MZMurad/X-band_Transmitter_Thesis_Files/Data/SpectrumAn_Data/2026-04-28_14-01-11_M2-022_Mixer_DownConv_LO-x_RF_-30dBm_Span_10MHz_RBW_100kHz.png

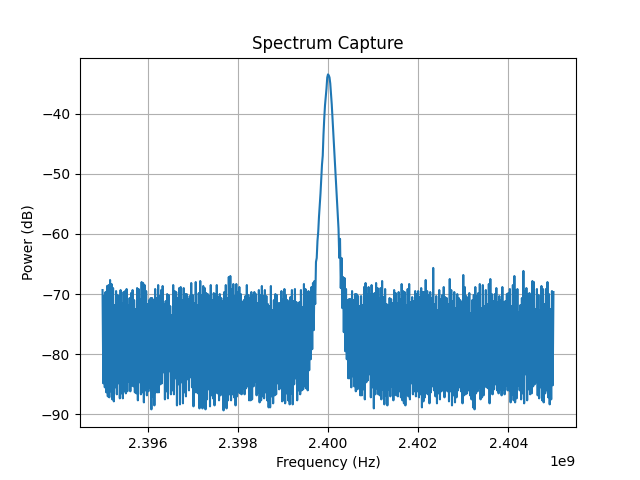
Data/SpectrumAn_Data/2026-04-28_14-01-11_M2-022_Mixer_DownConv_LO-x_RF_-30dBm_Span_10MHz_RBW_100kHz.png
