MZMurad/X-band_Transmitter_Thesis_Files/Data/SpectrumAn_Data/2026-04-28_14-03-07_M2-022_Mixer_LO_Span_10MHz_RBW_100kHz.png

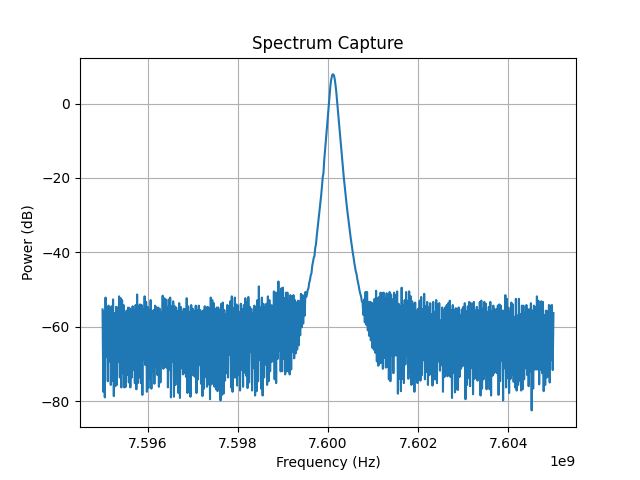
Data/SpectrumAn_Data/2026-04-28_14-03-07_M2-022_Mixer_LO_Span_10MHz_RBW_100kHz.png
