MZMurad/X-band_Transmitter_Thesis_Files/Data/SpectrumAn_Data/2026-04-28_14-05-14_M2-022_Mixer_RF_Span_10MHz_RBW_100kHz.png

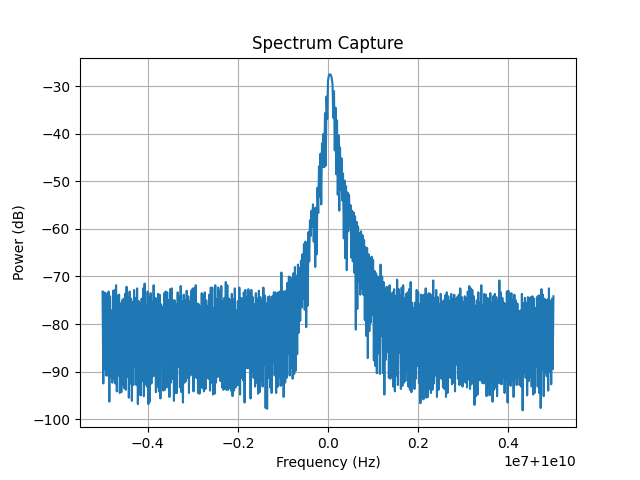
Data/SpectrumAn_Data/2026-04-28_14-05-14_M2-022_Mixer_RF_Span_10MHz_RBW_100kHz.png
