MZMurad/X-band_Transmitter_Thesis_Files/Data/SpectrumAn_Data/2026-04-28_14-42-43_Composite_Mixer_Span_Full_RBW_100kHz.png

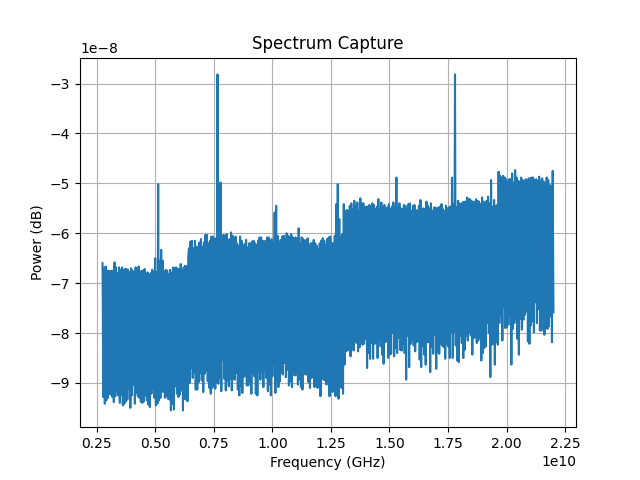
Data/SpectrumAn_Data/2026-04-28_14-42-43_Composite_Mixer_Span_Full_RBW_100kHz.png
