MZMurad/X-band_Transmitter_Thesis_Files/Data/SpectrumAn_Data/2026-04-28_14-44-34_Composite_Mixer_Span_500MHz_RBW_5MHz.png

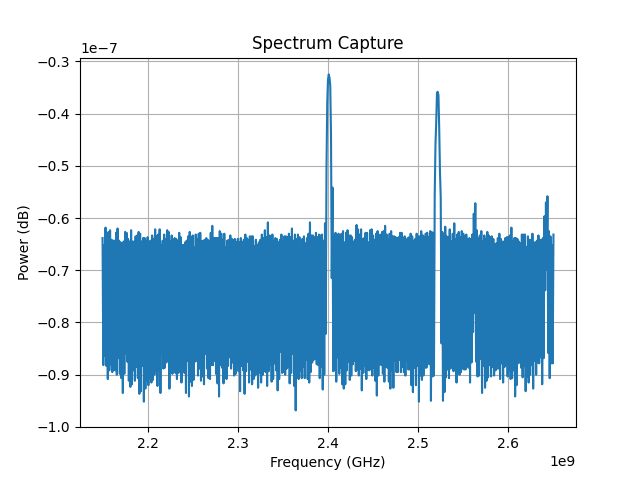
Data/SpectrumAn_Data/2026-04-28_14-44-34_Composite_Mixer_Span_500MHz_RBW_5MHz.png
