MZMurad/X-band_Transmitter_Thesis_Files/Data/SpectrumAn_Data/2026-04-28_14-51-12_Composite_Mixer_CW_IF_Span_10MHz_RBW_5MHz.png

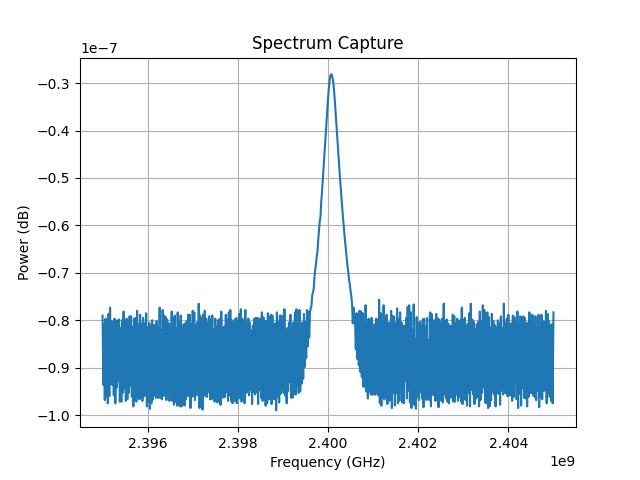
Data/SpectrumAn_Data/2026-04-28_14-51-12_Composite_Mixer_CW_IF_Span_10MHz_RBW_5MHz.png
