MZMurad/X-band_Transmitter_Thesis_Files/Data/SpectrumAn_Data/2026-04-28_14-57-12_Composite_Mixer_SDR_FullCapture_Span_1MHz_RBW_10kHz.png

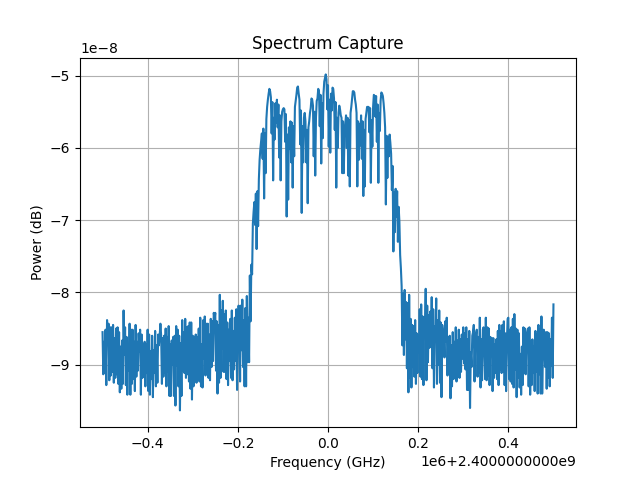
Data/SpectrumAn_Data/2026-04-28_14-57-12_Composite_Mixer_SDR_FullCapture_Span_1MHz_RBW_10kHz.png
