MZMurad/X-band_Transmitter_Thesis_Files/Data/SpectrumAn_Data/2026-04-28_16-52-47_PLL_Amp_LO_Span_Full_RBW_100kHz.png

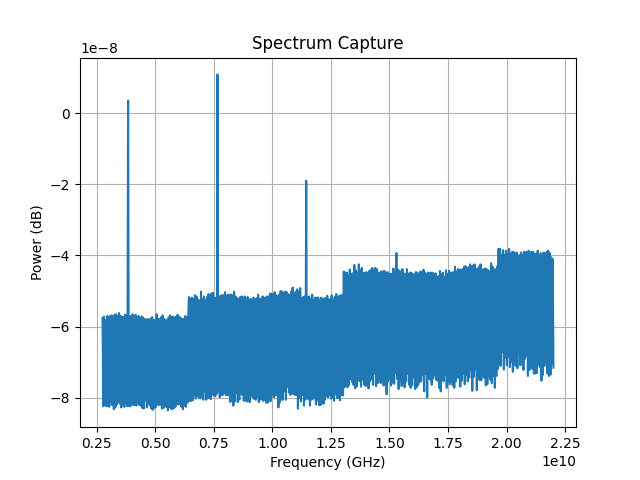
Data/SpectrumAn_Data/2026-04-28_16-52-47_PLL_Amp_LO_Span_Full_RBW_100kHz.png
