MZMurad/X-band_Transmitter_Thesis_Files/Data/SpectrumAn_Data/Mixer_Spectrum/2026-05-18_16-15-24_SDR_Upconverted_Spectrum.png

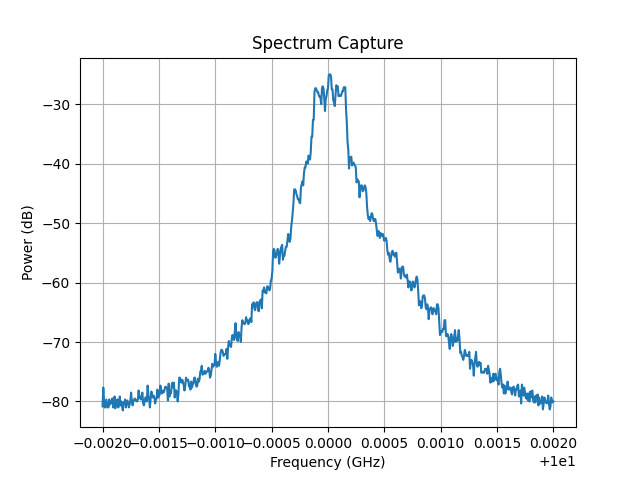
Data/SpectrumAn_Data/Mixer_Spectrum/2026-05-18_16-15-24_SDR_Upconverted_Spectrum.png
