MZMurad/X-band_Transmitter_Thesis_Files/Data/SpectrumAn_Data/Mixer_Spectrum/2026-05-18_16-33-44_SDR_Upconverted_Spectrum_Spa_1MHz_RBW30kHz.png

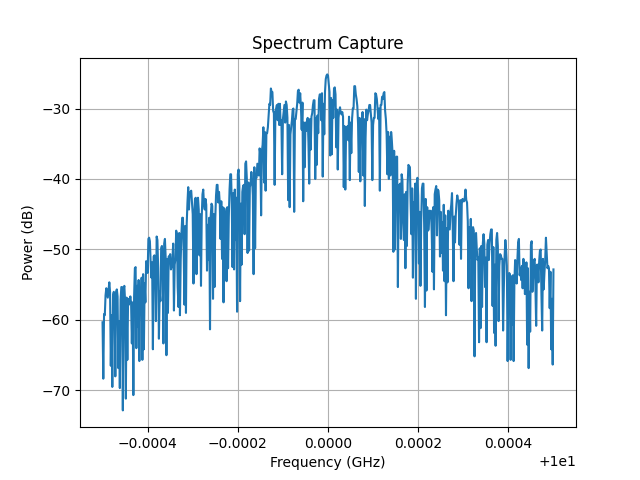
Data/SpectrumAn_Data/Mixer_Spectrum/2026-05-18_16-33-44_SDR_Upconverted_Spectrum_Spa_1MHz_RBW30kHz.png
