MZMurad/X-band_Transmitter_Thesis_Files/Data/SpectrumAn_Data/Mixer_Spectrum/2026-05-18_16-59-57_SDR_Composite_Mixer_Spectrum_Spa_1MHz_RBW_30kHz.png

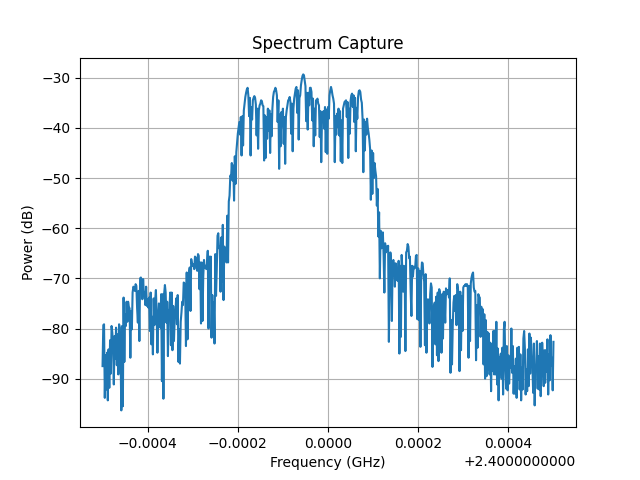
Data/SpectrumAn_Data/Mixer_Spectrum/2026-05-18_16-59-57_SDR_Composite_Mixer_Spectrum_Spa_1MHz_RBW_30kHz.png
