MZMurad/X-band_Transmitter_Thesis_Files/Data/SpectrumAn_Data/Mixer_Spectrum/2026-05-18_17-08-34_SDR_Composite_Mixer_Spectrum_Spa_1MHz_RBW_10kHz.png

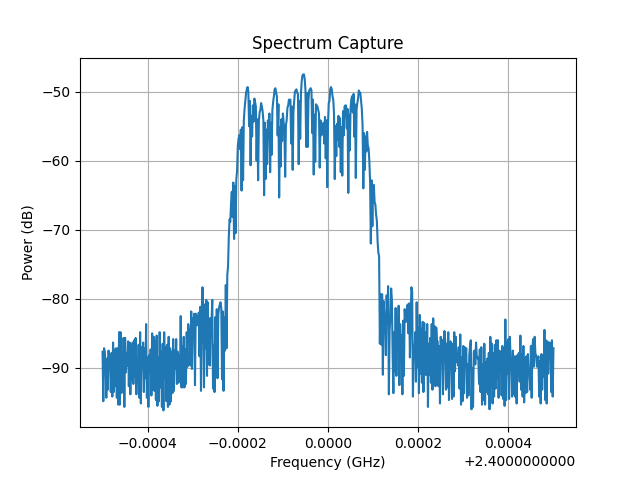
Data/SpectrumAn_Data/Mixer_Spectrum/2026-05-18_17-08-34_SDR_Composite_Mixer_Spectrum_Spa_1MHz_RBW_10kHz.png
