MZMurad/X-band_Transmitter_Thesis_Files/Data/SpectrumAn_Data/Mixer_Spectrum/2026-05-18_17-30-45_Mixer_CW_Spectrum_Spa_6GHz_RBW_100kHz.png

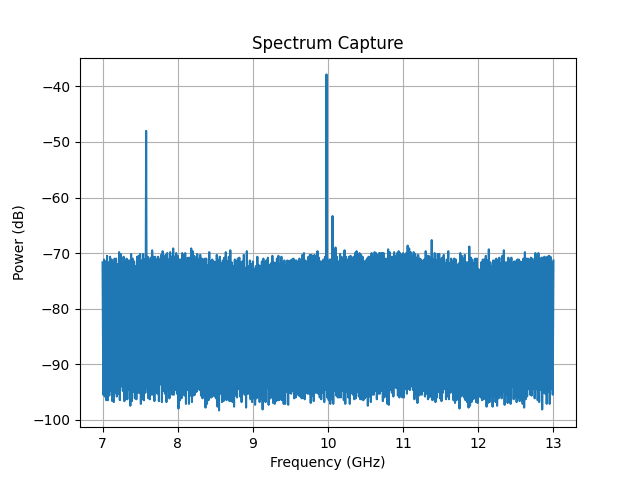
Data/SpectrumAn_Data/Mixer_Spectrum/2026-05-18_17-30-45_Mixer_CW_Spectrum_Spa_6GHz_RBW_100kHz.png
