MZMurad/X-band_Transmitter_Thesis_Files/Data/SpectrumAn_Data/PLL_Filter_Test/SDR_Test/2026-05-12_14-50-37_TX_SDR_Spectrum.png

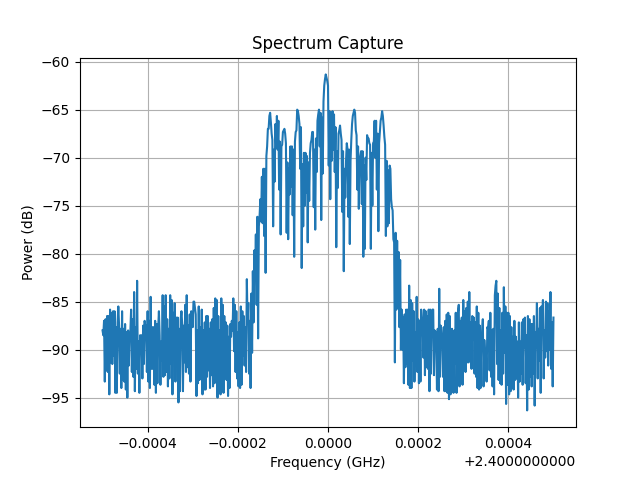
Data/SpectrumAn_Data/PLL_Filter_Test/SDR_Test/2026-05-12_14-50-37_TX_SDR_Spectrum.png
