MZMurad/X-band_Transmitter_Thesis_Files/Data/SpectrumAn_Data/PLL_Span_50MHz_RBW_3kHz.png

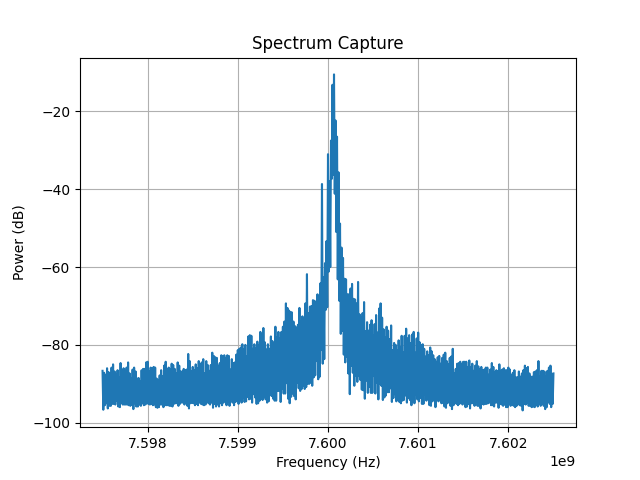
Data/SpectrumAn_Data/PLL_Span_50MHz_RBW_3kHz.png
