MZMurad/X-band_Transmitter_Thesis_Files/Data/SpectrumAn_Data/QPSK_Test/2026-05-31_18-19-41_SDR_Spectrum_Spa_5MHz_RBW_30kHz_MAXHOLD.png

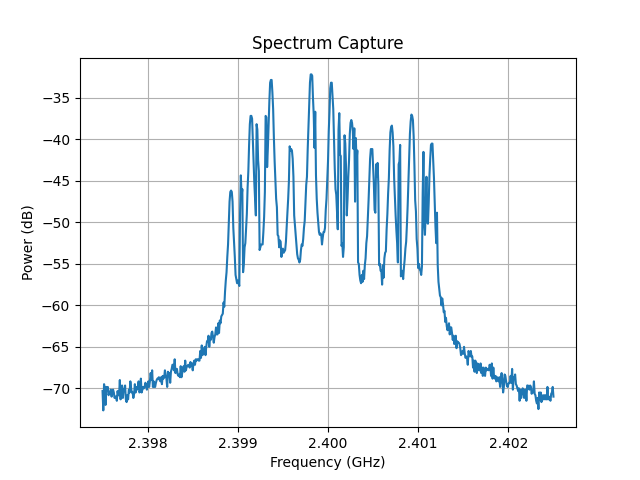
Data/SpectrumAn_Data/QPSK_Test/2026-05-31_18-19-41_SDR_Spectrum_Spa_5MHz_RBW_30kHz_MAXHOLD.png
