MZMurad/X-band_Transmitter_Thesis_Files/Data/VNA_Capture/2X10dBAtten.png

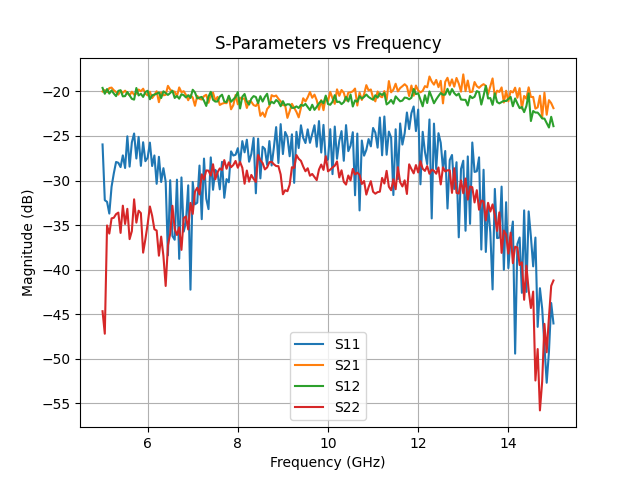
Data/VNA_Capture/2X10dBAtten.png
