MZMurad/X-band_Transmitter_Thesis_Files/Data/VNA_Capture/10dB_CalKit_Atten.png

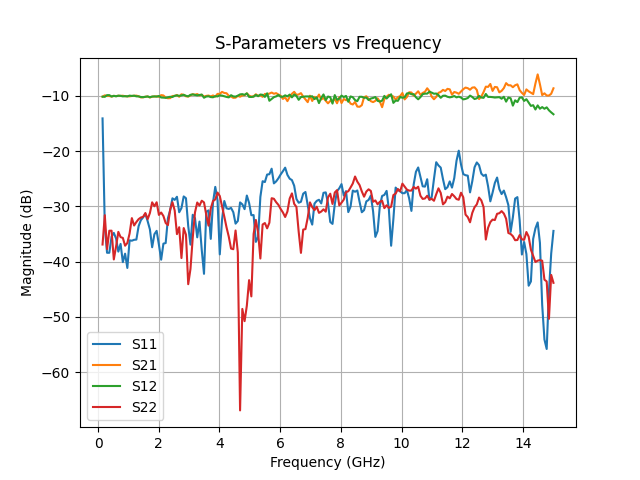
Data/VNA_Capture/10dB_CalKit_Atten.png
