MZMurad/X-band_Transmitter_Thesis_Files/Data/SpectrumAn_Data/2026-04-05_14-34-03_TestSpectrumCapture.csv

Date: 2026-04-05_14-34-03
Center Frequency (Hz): 7600000000.0
Span (Hz): 9700000000.0
RBW (Hz): 2000000.0
ID: 8562A GPIB0::18::INSTR
Frequency (Hz) | Power (dBm)
2.750000000000000000e+09 | -4.382999999999999829e+01
2.766166666666666508e+09 | -7.132999999999999829e+01
2.782333333333333492e+09 | -4.415999999999999659e+01
2.798500000000000000e+09 | -7.215999999999999659e+01
2.814666666666666508e+09 | -4.315999999999999659e+01
2.830833333333333492e+09 | -7.215999999999999659e+01
2.847000000000000000e+09 | -4.300000000000000000e+01
2.863166666666666508e+09 | -7.065999999999999659e+01
2.879333333333333492e+09 | -4.350000000000000000e+01
2.895500000000000000e+09 | -7.432999999999999829e+01
2.911666666666666508e+09 | -4.265999999999999659e+01
2.927833333333333492e+09 | -7.565999999999999659e+01
2.944000000000000000e+09 | -4.165999999999999659e+01
2.960166666666666508e+09 | -7.350000000000000000e+01
2.976333333333333492e+09 | -4.382999999999999829e+01
2.992500000000000000e+09 | -7.300000000000000000e+01
3.008666666666666508e+09 | -4.432999999999999829e+01
3.024833333333333492e+09 | -7.315999999999999659e+01
3.041000000000000000e+09 | -4.482999999999999829e+01
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
