MZMurad/X-band_Transmitter_Thesis_Files/Data/SpectrumAn_Data/PLL_Filter_Test/2026-05-12_14-18-42_PLL_PAmp_Test_Filter_Span_9.7GHz_RBW_2MHz_Distortion_Issue.csv

Date: 2026-05-12_14-18-42
Center Frequency (Hz): 7600000000.0
Span (Hz): 9700000000.0
RBW (Hz): 2000000.0
ID: 8562A GPIB0::18::INSTR
Frequency (Hz) | Power (dBm)
2.750000000000000000e+09 | -4.265999999999999659e+01
2.766166666666666508e+09 | -7.150000000000000000e+01
2.782333333333333492e+09 | -4.365999999999999659e+01
2.798500000000000000e+09 | -7.365999999999999659e+01
2.814666666666666508e+09 | -4.315999999999999659e+01
2.830833333333333492e+09 | -7.350000000000000000e+01
2.847000000000000000e+09 | -4.200000000000000000e+01
2.863166666666666508e+09 | -7.065999999999999659e+01
2.879333333333333492e+09 | -4.350000000000000000e+01
2.895500000000000000e+09 | -6.832999999999999829e+01
2.911666666666666508e+09 | -4.215999999999999659e+01
2.927833333333333492e+09 | -7.082999999999999829e+01
2.944000000000000000e+09 | -4.082999999999999829e+01
2.960166666666666508e+09 | -7.282999999999999829e+01
2.976333333333333492e+09 | -4.365999999999999659e+01
2.992500000000000000e+09 | -7.265999999999999659e+01
3.008666666666666508e+09 | -4.315999999999999659e+01
3.024833333333333492e+09 | -7.250000000000000000e+01
3.041000000000000000e+09 | -4.365999999999999659e+01
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
