MZMurad/X-band_Transmitter_Thesis_Files/Data/SpectrumAn_Data/PLL_Filter_Test/2026-05-12_14-36-30_PLL_PAmp_PFILTER_BeforeAmp_Test_Filter_Span_9.7GHz_RBW_2MHz_Distortion_Issue.csv

Date: 2026-05-12_14-36-30
Center Frequency (Hz): 7600000000.0
Span (Hz): 9700000000.0
RBW (Hz): 2000000.0
ID: 8562A GPIB0::18::INSTR
Frequency (Hz) | Power (dBm)
2.750000000000000000e+09 | -4.332999999999999829e+01
2.766166666666666508e+09 | -6.850000000000000000e+01
2.782333333333333492e+09 | -4.350000000000000000e+01
2.798500000000000000e+09 | -7.015999999999999659e+01
2.814666666666666508e+09 | -4.100000000000000000e+01
2.830833333333333492e+09 | -6.815999999999999659e+01
2.847000000000000000e+09 | -4.300000000000000000e+01
2.863166666666666508e+09 | -7.132999999999999829e+01
2.879333333333333492e+09 | -4.332999999999999829e+01
2.895500000000000000e+09 | -7.165999999999999659e+01
2.911666666666666508e+09 | -4.215999999999999659e+01
2.927833333333333492e+09 | -7.115999999999999659e+01
2.944000000000000000e+09 | -4.250000000000000000e+01
2.960166666666666508e+09 | -6.900000000000000000e+01
2.976333333333333492e+09 | -4.182999999999999829e+01
2.992500000000000000e+09 | -7.182999999999999829e+01
3.008666666666666508e+09 | -4.350000000000000000e+01
3.024833333333333492e+09 | -7.150000000000000000e+01
3.041000000000000000e+09 | -4.300000000000000000e+01
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
