MZMurad/X-band_Transmitter_Thesis_Files/Data/SpectrumAn_Data/PLL_Filter_Test/2026-05-12_14-36-30_PLL_PAmp_PFILTER_BeforeAmp_Test_Filter_Span_9.7GHz_RBW_2MHz_Distortion_Issue.png

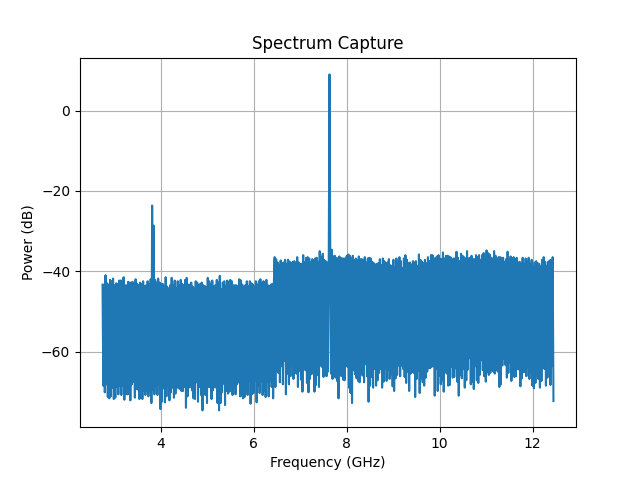
Data/SpectrumAn_Data/PLL_Filter_Test/2026-05-12_14-36-30_PLL_PAmp_PFILTER_BeforeAmp_Test_Filter_Span_9.7GHz_RBW_2MHz_Distortion_Issue.png
