MZMurad/X-band_Transmitter_Thesis_Files/Data/VNA_Capture/Amplifier_Test1_NoAtten_Pin_-25dB.png

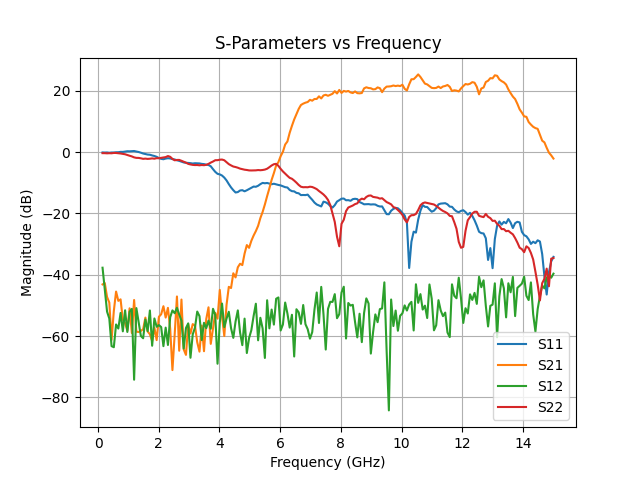
Data/VNA_Capture/Amplifier_Test1_NoAtten_Pin_-25dB.png
