MZMurad/X-band_Transmitter_Thesis_Files/Data/VNA_Capture/Amplifier_Test2_Atten_-10dB_Pin_-10dB.png

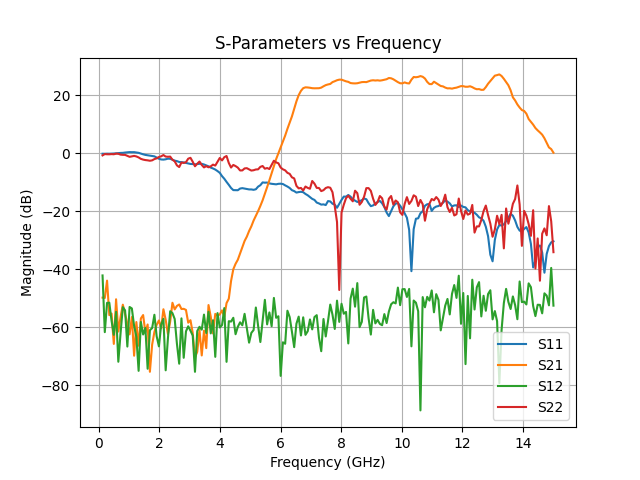
Data/VNA_Capture/Amplifier_Test2_Atten_-10dB_Pin_-10dB.png
