MZMurad/X-band_Transmitter_Thesis_Files/Data/VNA_Capture/Amplifier_Testt3_Pin_-10dB.png

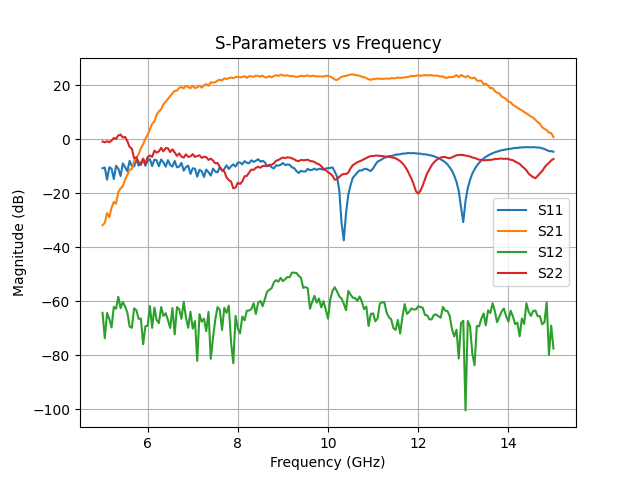
Data/VNA_Capture/Amplifier_Testt3_Pin_-10dB.png
