MZMurad/X-band_Transmitter_Thesis_Files/Data/SpectrumAn_Data/2026-04-28_17-56-01_PLL_Amp_LO_Span_9.7GHz_RBW_100kHz_Harmonics_Issue.png

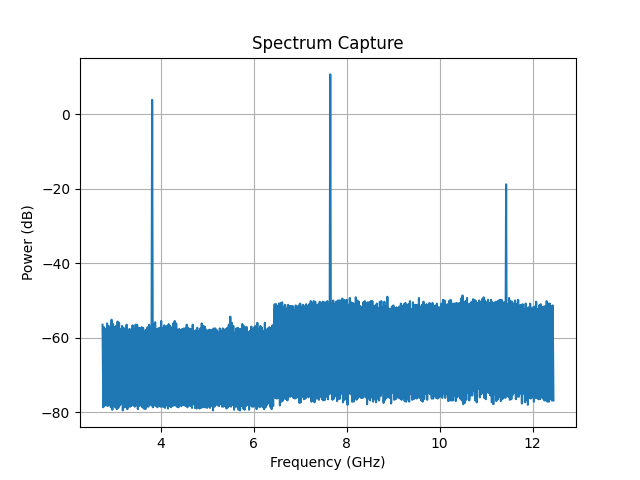
Data/SpectrumAn_Data/2026-04-28_17-56-01_PLL_Amp_LO_Span_9.7GHz_RBW_100kHz_Harmonics_Issue.png
