MZMurad/X-band_Transmitter_Thesis_Files/Data/SpectrumAn_Data/2026-04-28_18-13-17_PLL_Mixer_SDR_Issue_Span_14GHz_RBW_30kHz_Harmonics_Issue.png

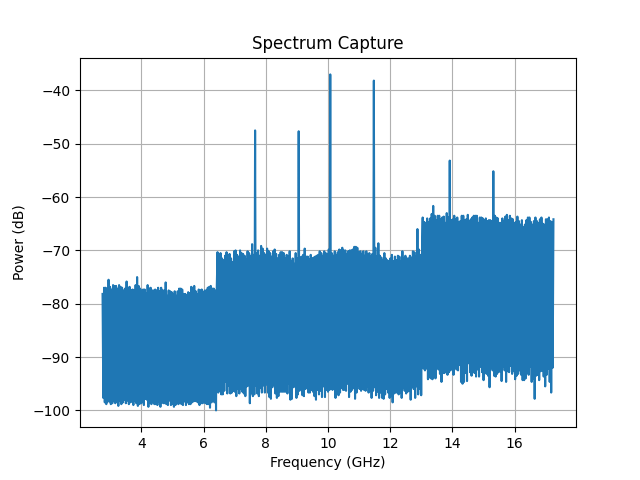
Data/SpectrumAn_Data/2026-04-28_18-13-17_PLL_Mixer_SDR_Issue_Span_14GHz_RBW_30kHz_Harmonics_Issue.png
